jrddupont/Orrery/3D Parts/Collar 3.stl

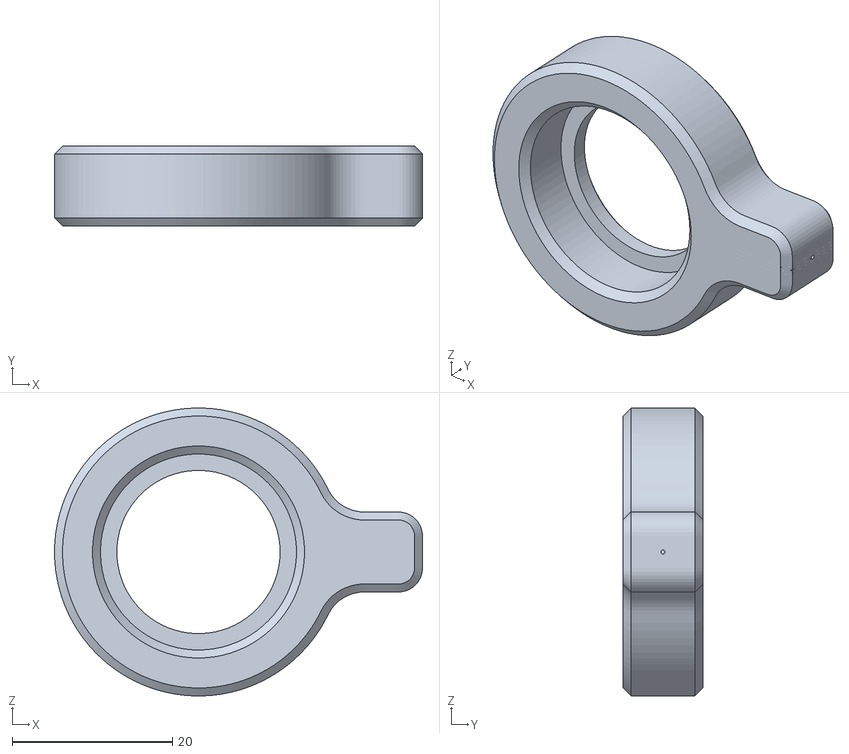
[picture p15: CAD file, 2018-05-02]
3D Parts/Collar 3.stl
46.0 x 10.0 x 36.0
