jrddupont/Orrery/3D Parts/Sun Upper.stl

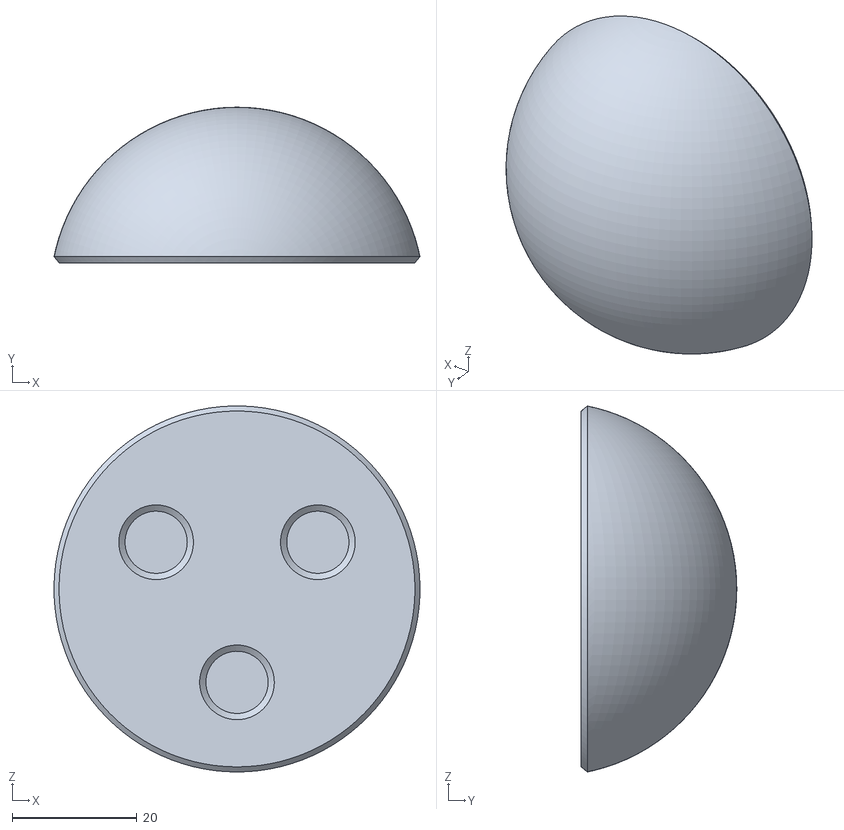
[picture p16: CAD file, 2018-05-02]
3D Parts/Sun Upper.stl
58.8 x 25.0 x 58.8
