jrddupont/Orrery/3D Parts/Shaft 3.stl

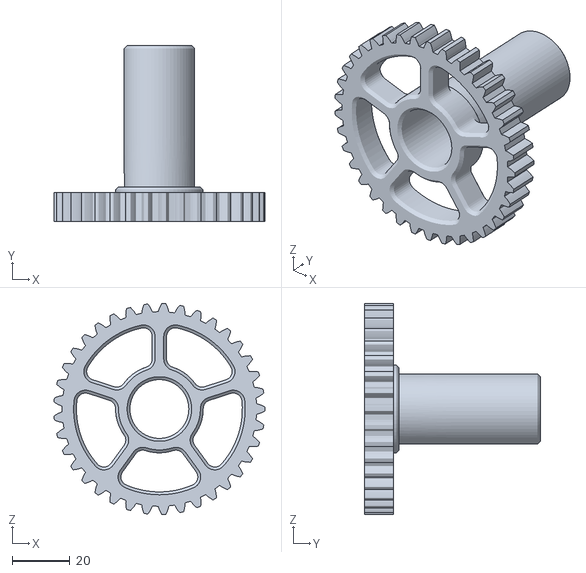
[picture p17: CAD file, 2018-05-02]
3D Parts/Shaft 3.stl
73.2 x 61.0 x 73.2
